harry123180/AUOProject/photo/1651546113493.jpg

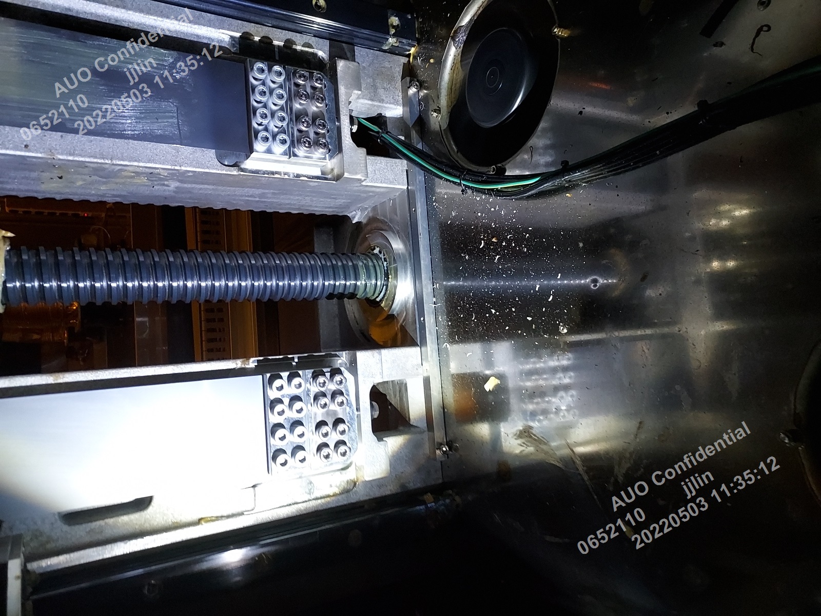
photo/1651546113493.jpg
