harry123180/AUOProject/photo/1651546139501.jpg

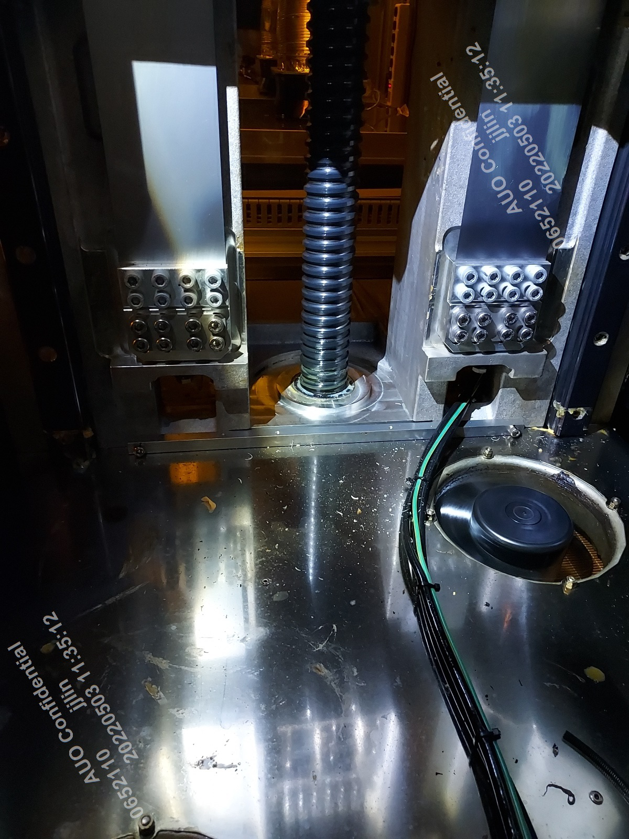
photo/1651546139501.jpg
