harry123180/AUOProject/photo/1651546161636.jpg

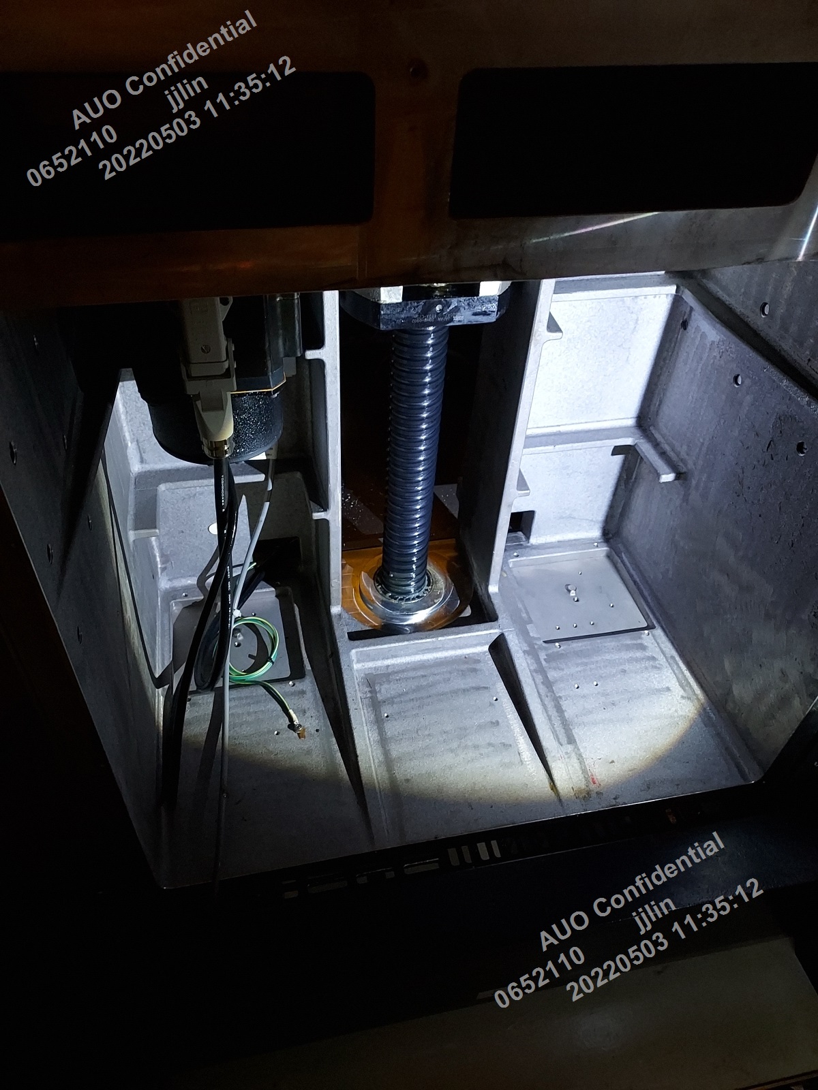
photo/1651546161636.jpg
