harry123180/AUOProject/photo/1651546175267.jpg

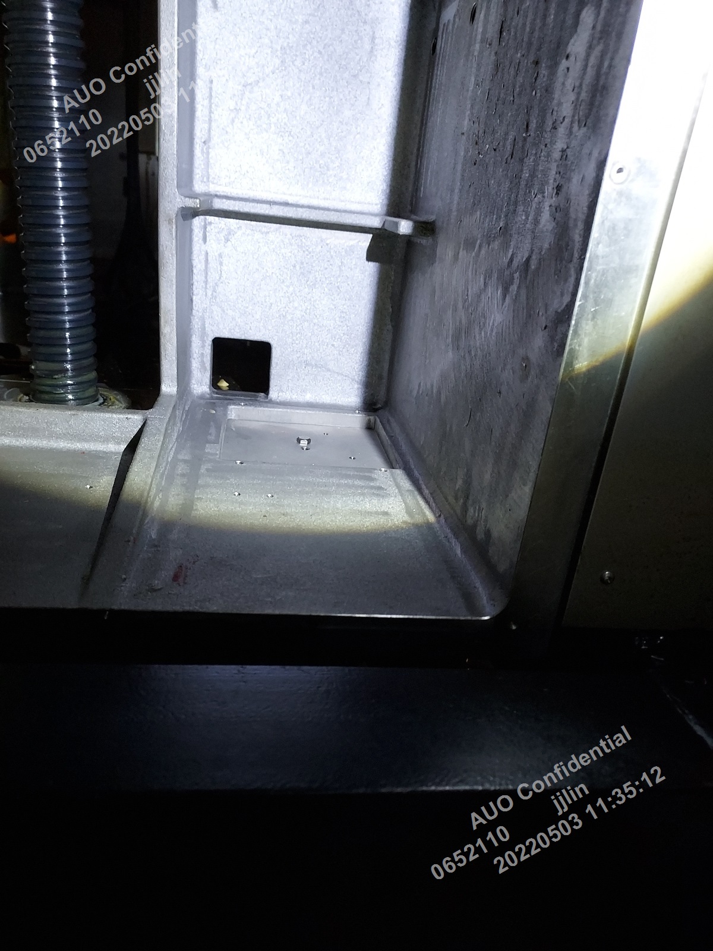
photo/1651546175267.jpg
