harry123180/AUOProject/photo/1651547614620.jpg

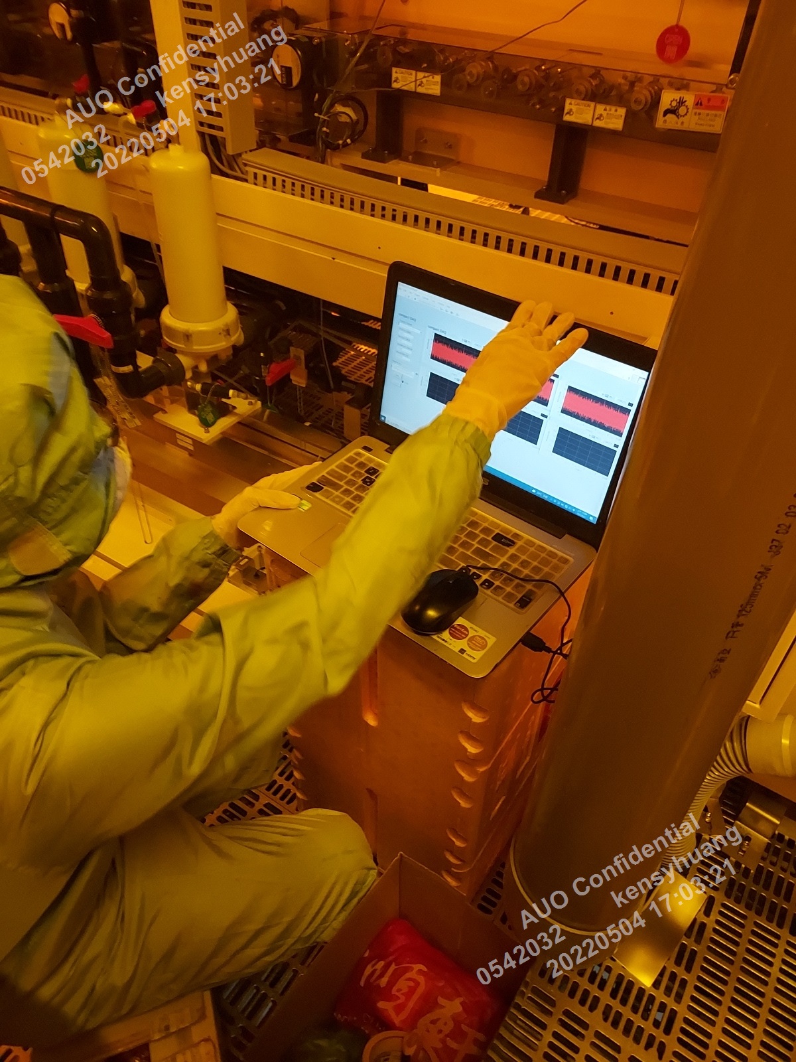
photo/1651547614620.jpg
