harry123180/AUOProject/photo/1651548057626.jpg

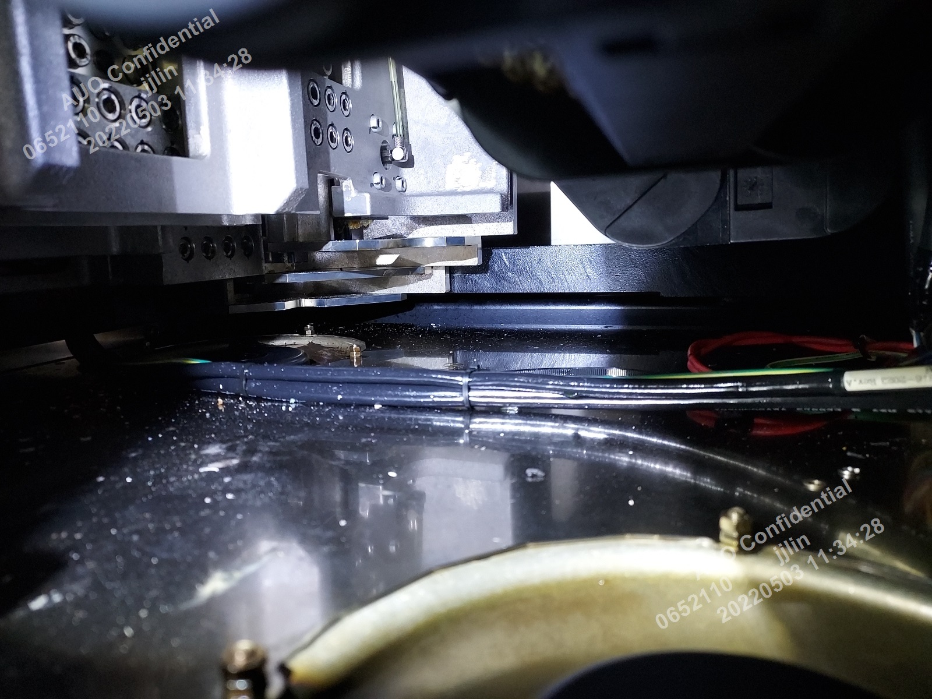
photo/1651548057626.jpg
