harry123180/AUOProject/photo/1651548065328.jpg

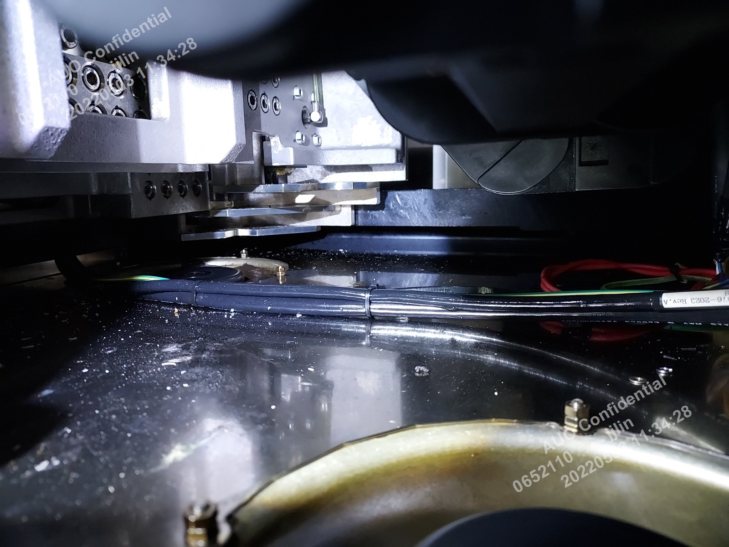
photo/1651548065328.jpg
