harry123180/AUOProject/photo/1651548679285.jpg

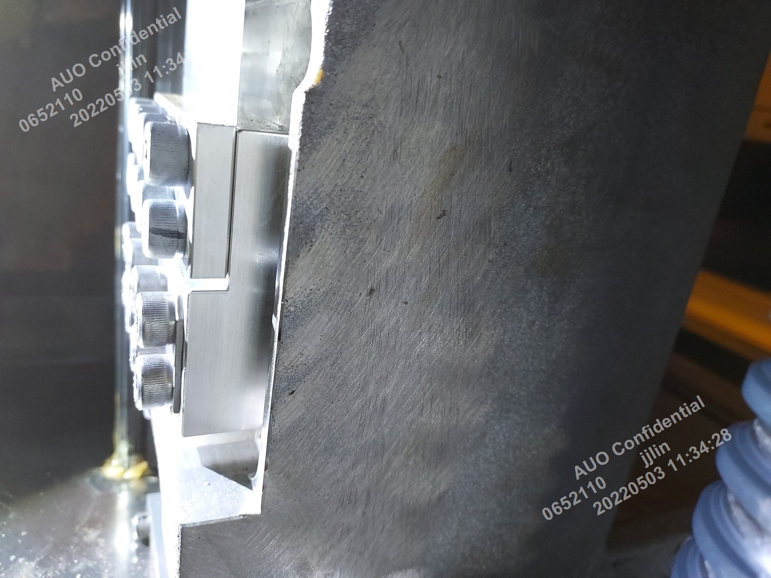
photo/1651548679285.jpg
