harry123180/AUOProject/photo/1651548737667.jpg

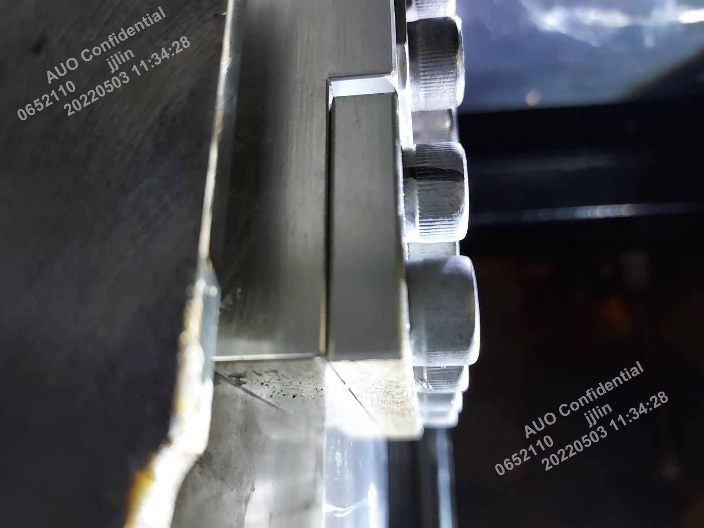
photo/1651548737667.jpg
