harry123180/AUOProject/photo/1651548792946.jpg

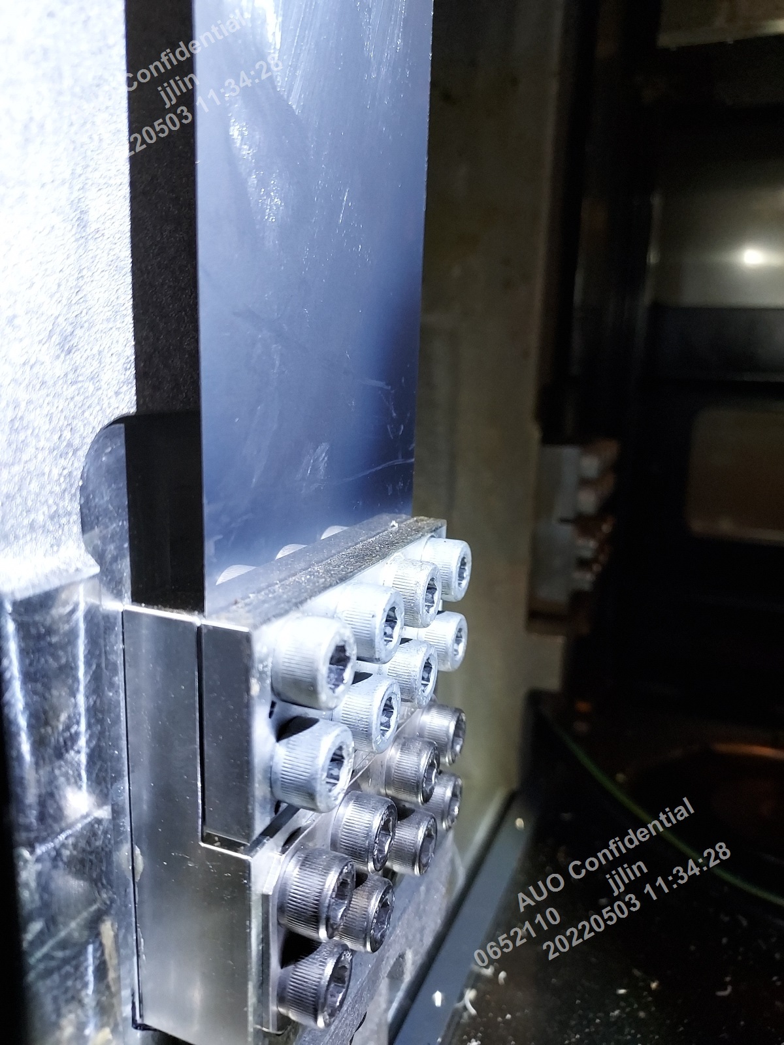
photo/1651548792946.jpg
