harry123180/AUOProject/photo/1651548812156.jpg

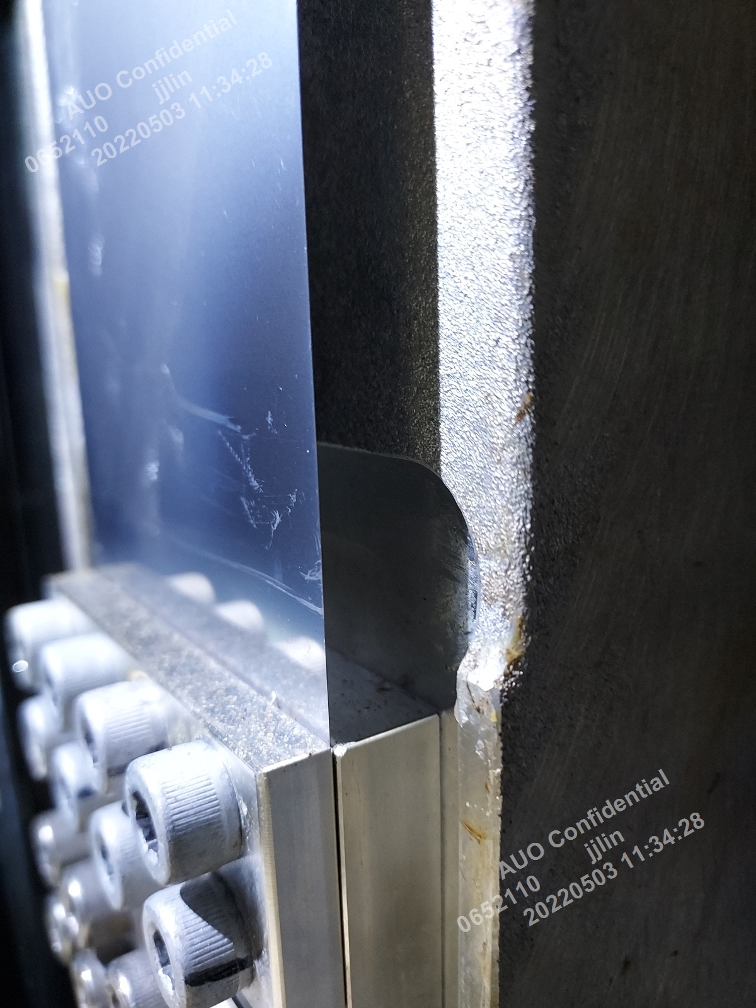
photo/1651548812156.jpg
