harry123180/AUOProject/photo/1651548824308.jpg

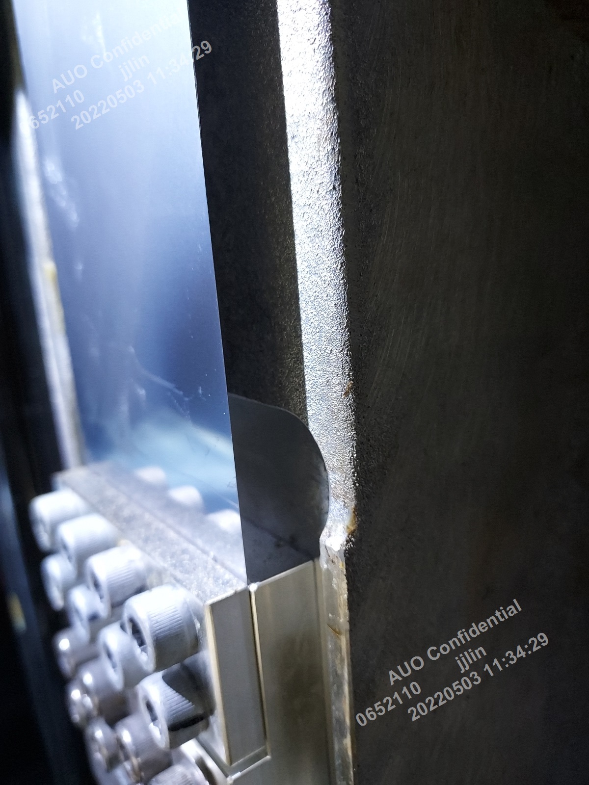
photo/1651548824308.jpg
