harry123180/AUOProject/photo/1651548843207.jpg

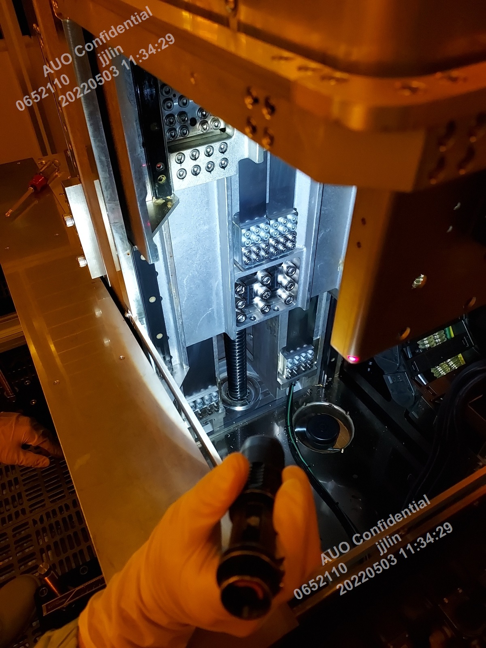
photo/1651548843207.jpg
