harry123180/AUOProject/photo/1651548852555.jpg

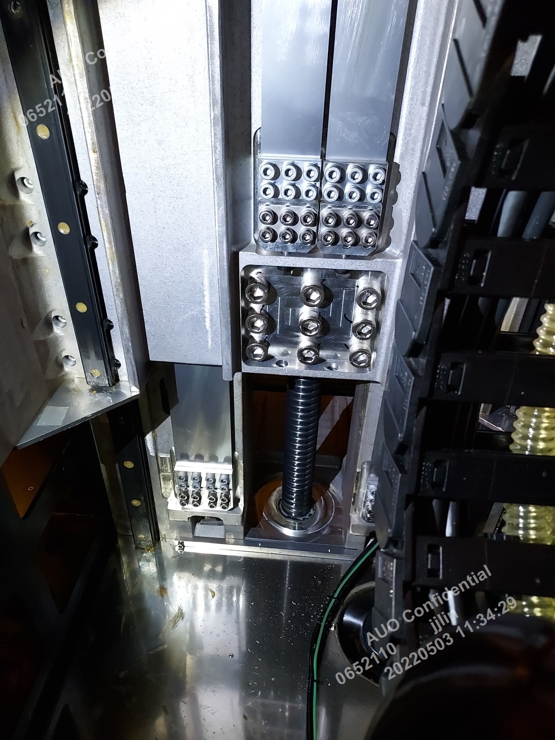
photo/1651548852555.jpg
