harry123180/AUOProject/photo/1651548869333.jpg

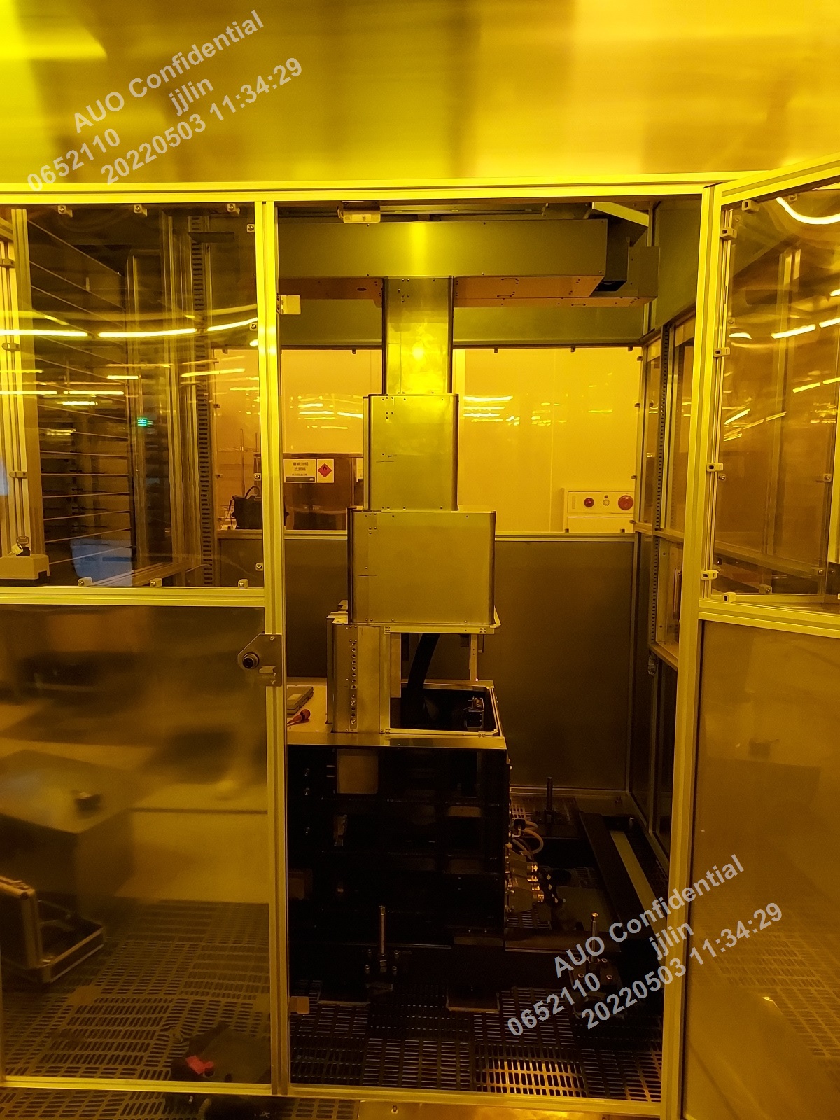
photo/1651548869333.jpg
