harry123180/AUOProject/photo/1651549266964.jpg

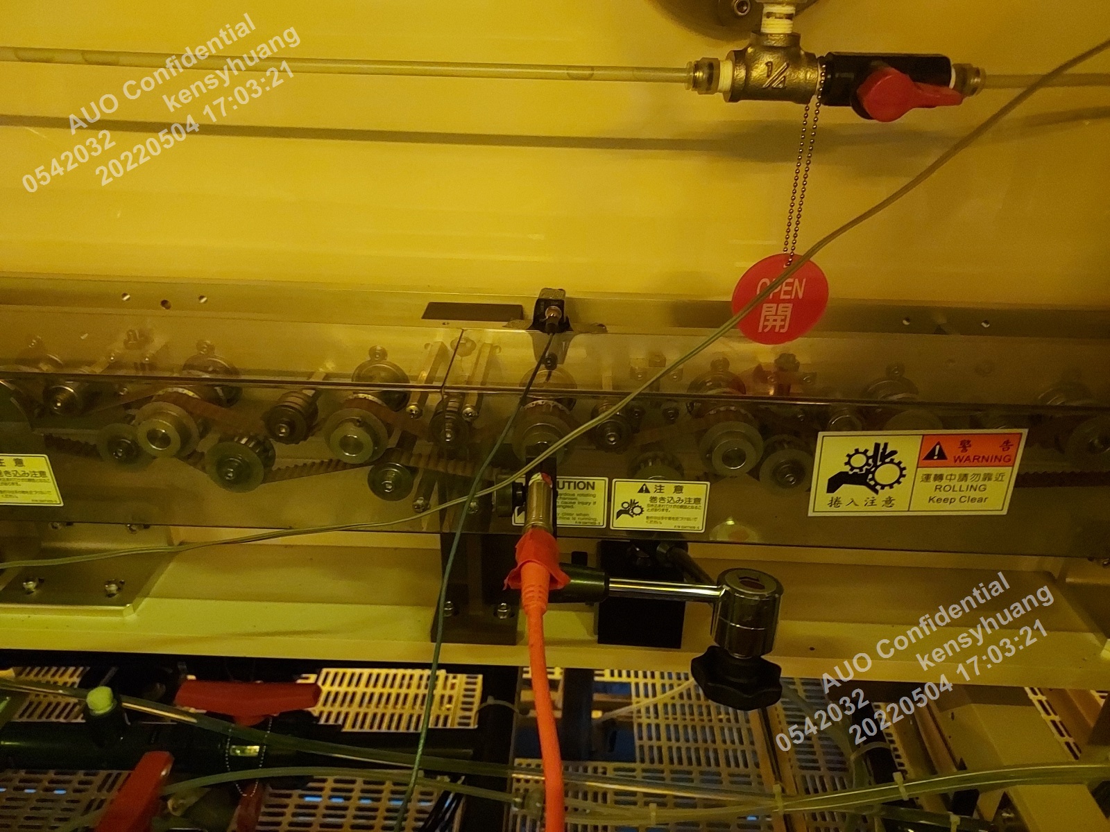
photo/1651549266964.jpg
