harry123180/AUOProject/photo/1651557246759.jpg

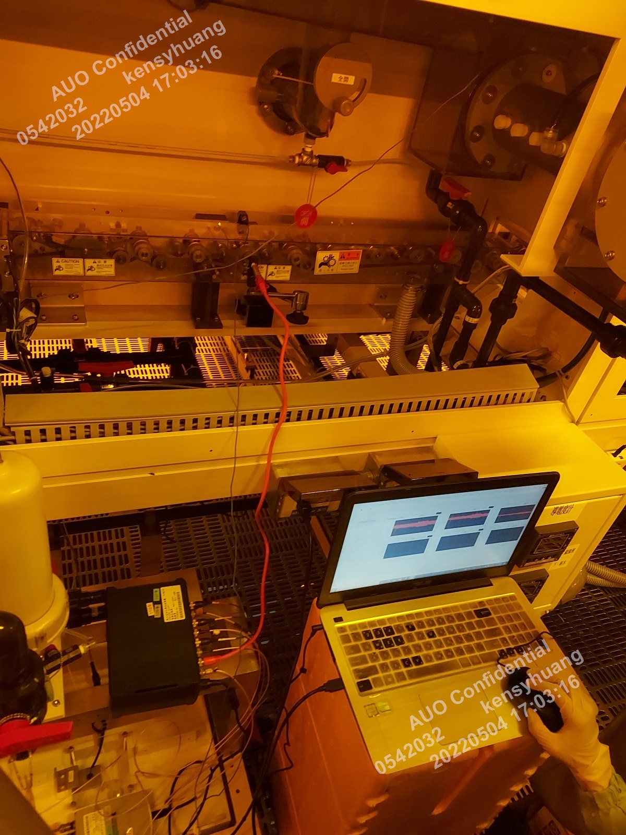
photo/1651557246759.jpg
