harry123180/AUOProject/photo/1651557253789.jpg

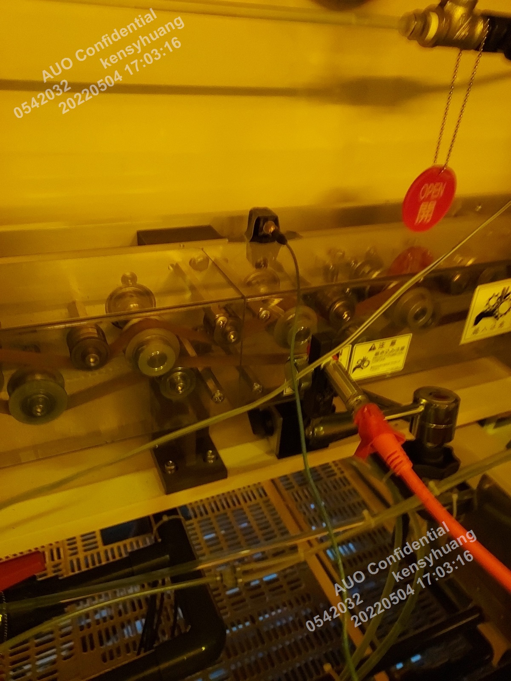
photo/1651557253789.jpg
