harry123180/AUOProject/photo/1651558922676.jpg

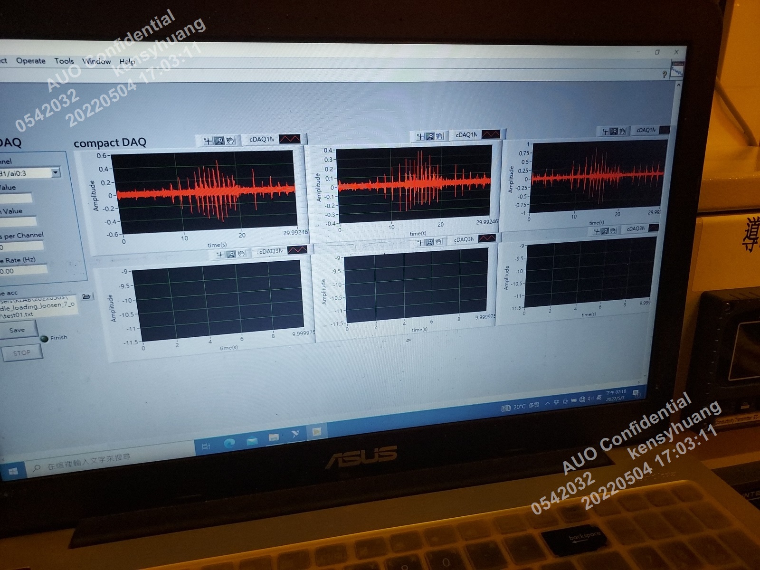
photo/1651558922676.jpg
