harry123180/AUOProject/photo/1651559129728.jpg

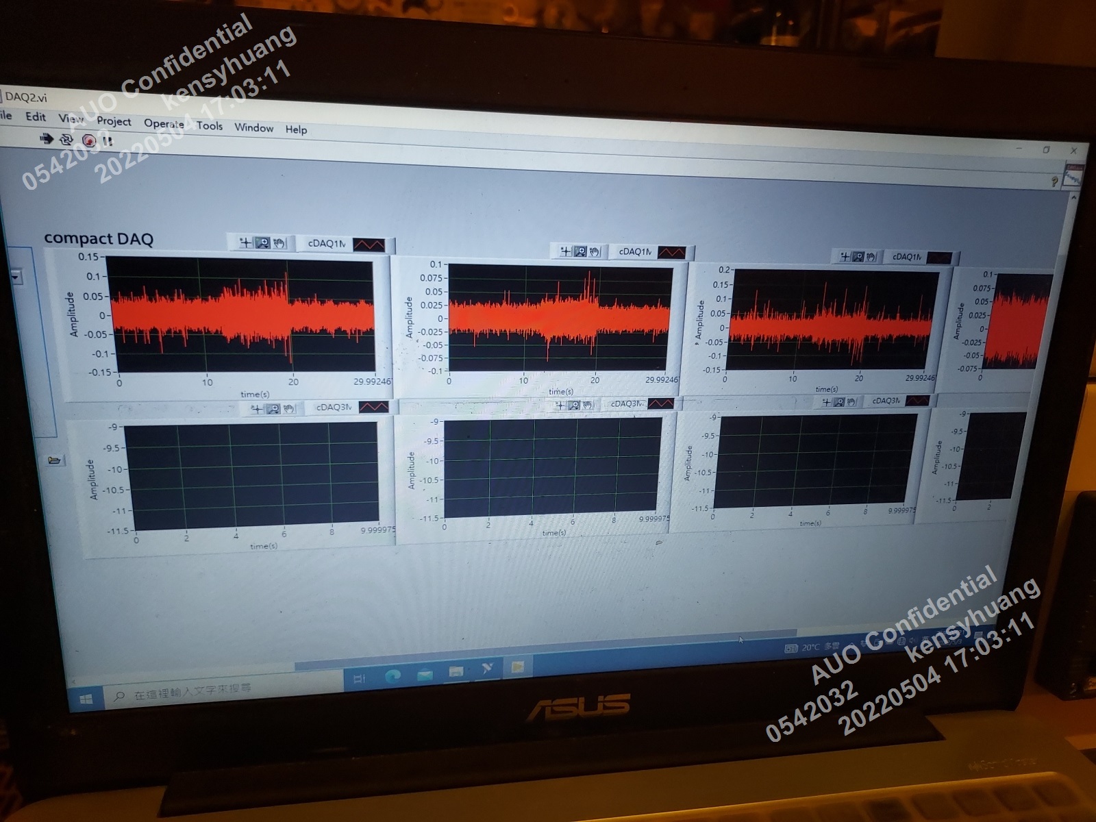
photo/1651559129728.jpg
