harry123180/AUOProject/photo/1651559417045.jpg

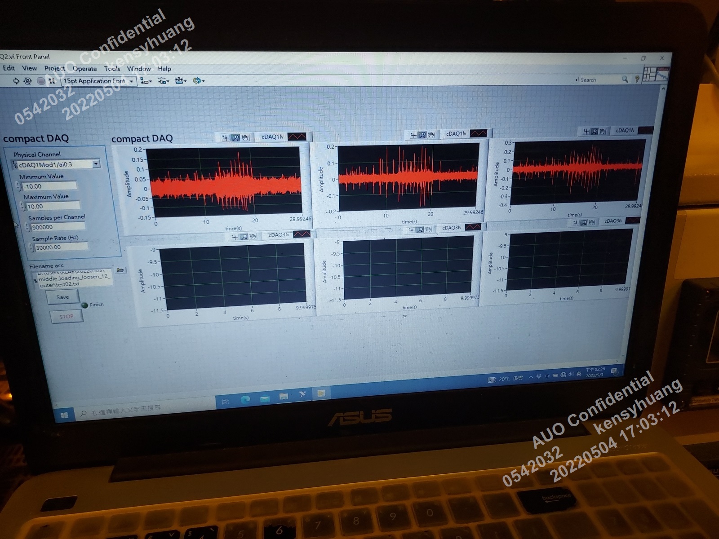
photo/1651559417045.jpg
