harry123180/AUOProject/photo/1651561638030.jpg

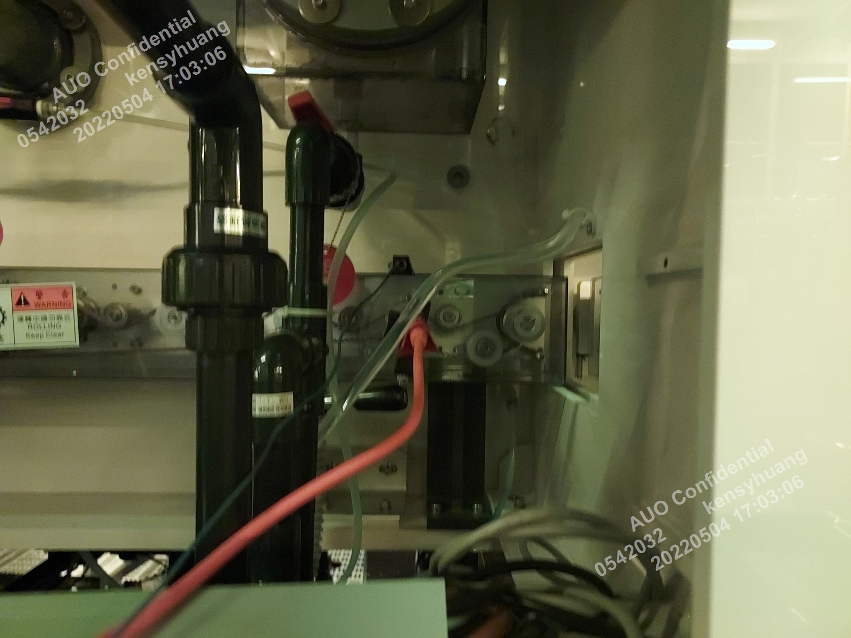
photo/1651561638030.jpg
