harry123180/AUOProject/photo/1651564419721.jpg

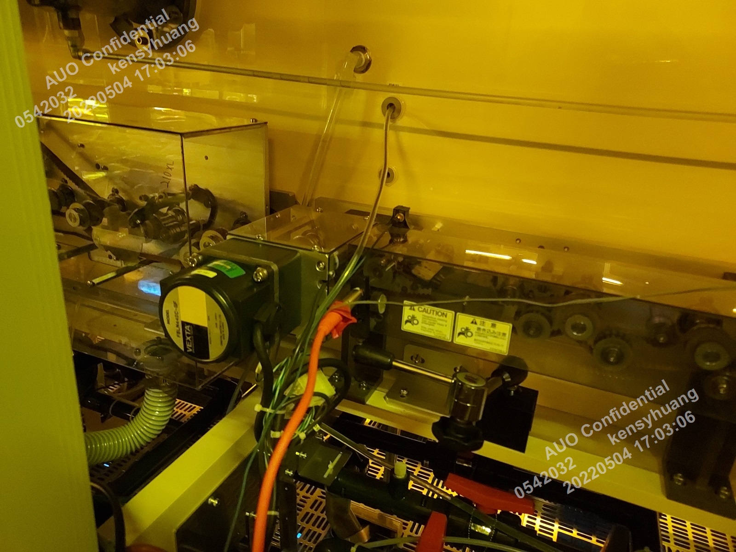
photo/1651564419721.jpg
