harry123180/AUOProject/數據分析圖/C1T.png

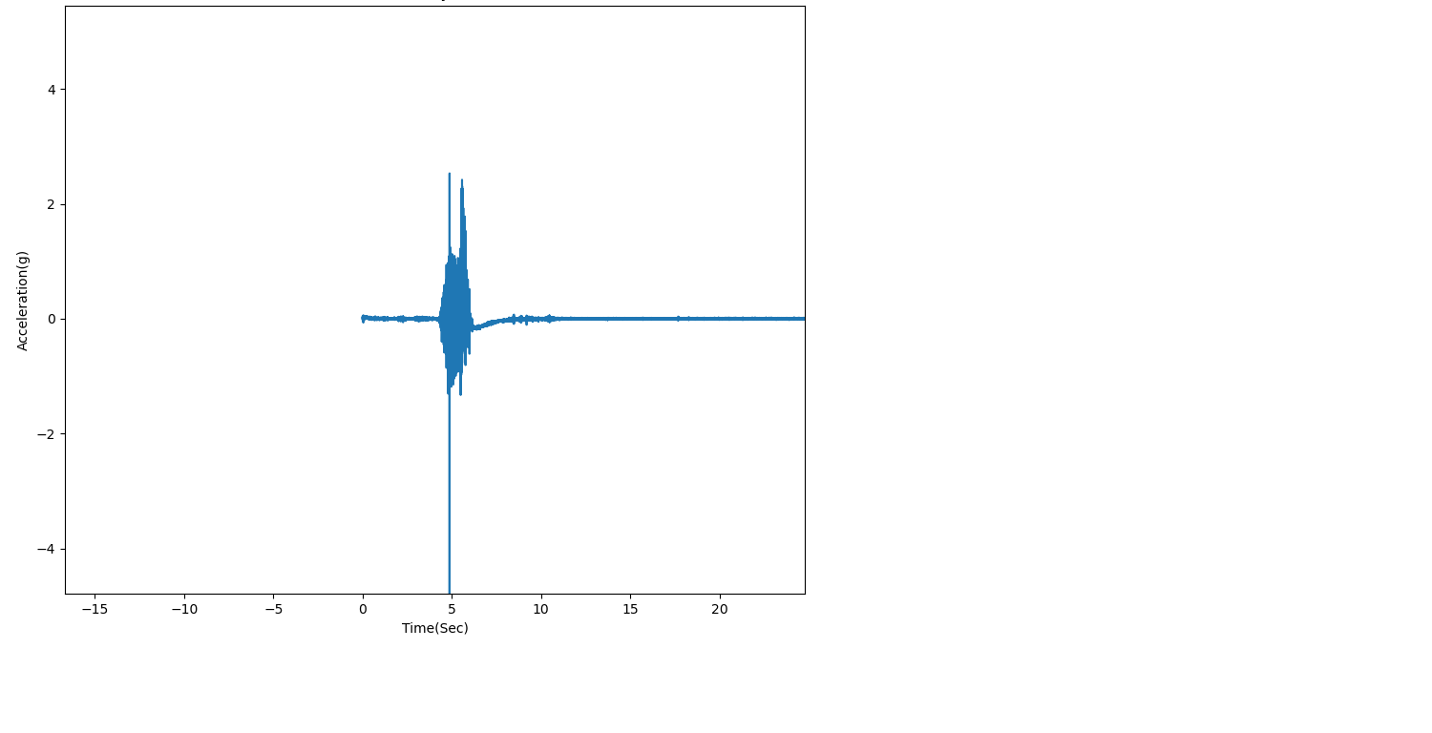
數據分析圖/C1T.png
