harry123180/AUOProject/數據分析圖/C1T_0_30.png

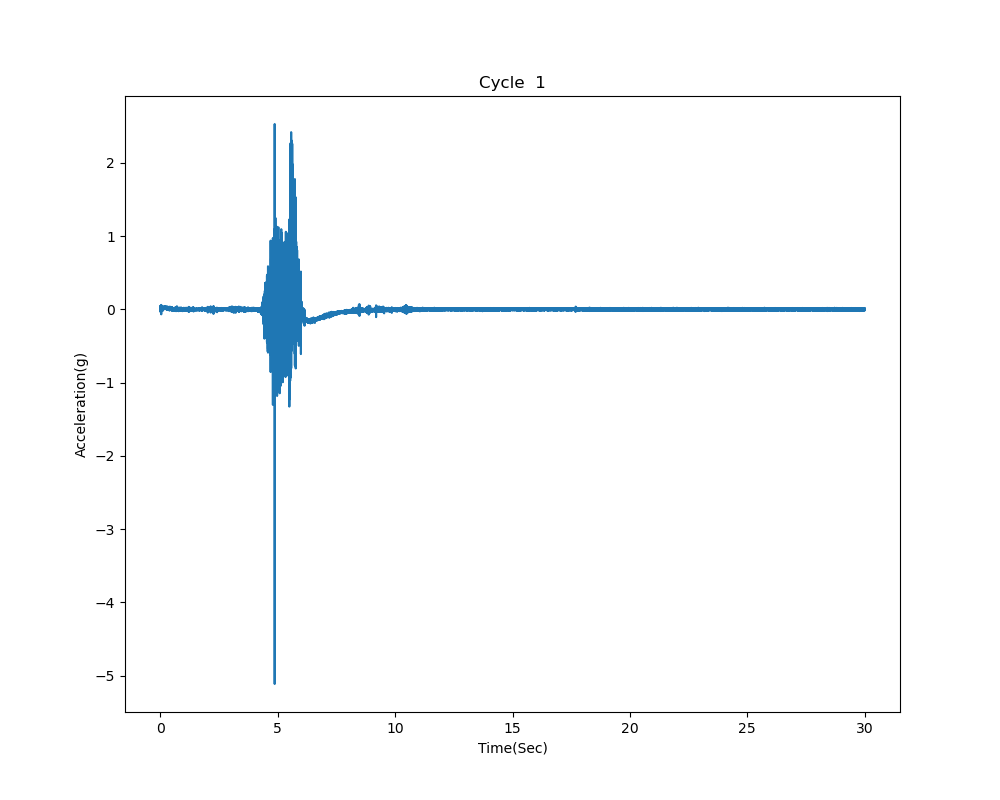
數據分析圖/C1T_0_30.png
