harry123180/AUOProject/數據分析圖/C2_C7_FFT_Mix.png

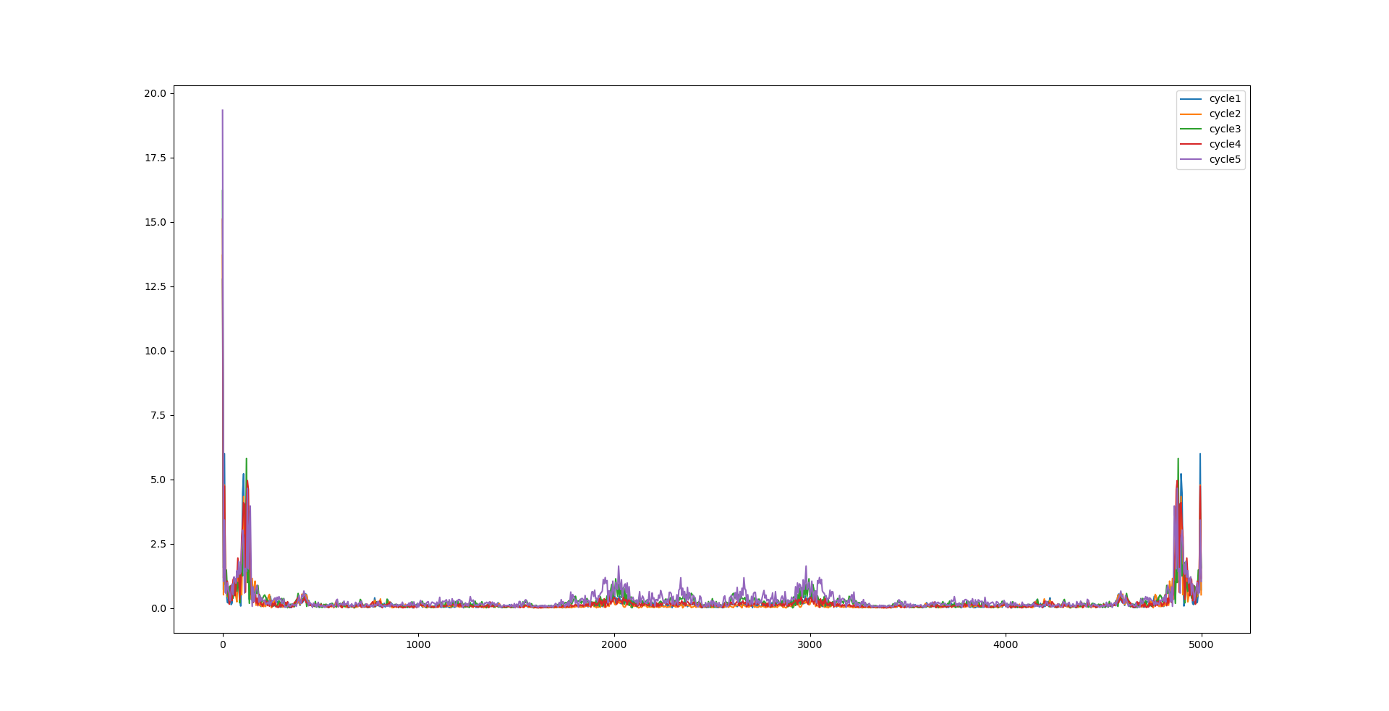
數據分析圖/C2_C7_FFT_Mix.png
