harry123180/AUOProject/數據分析圖/C2T_30_76.png

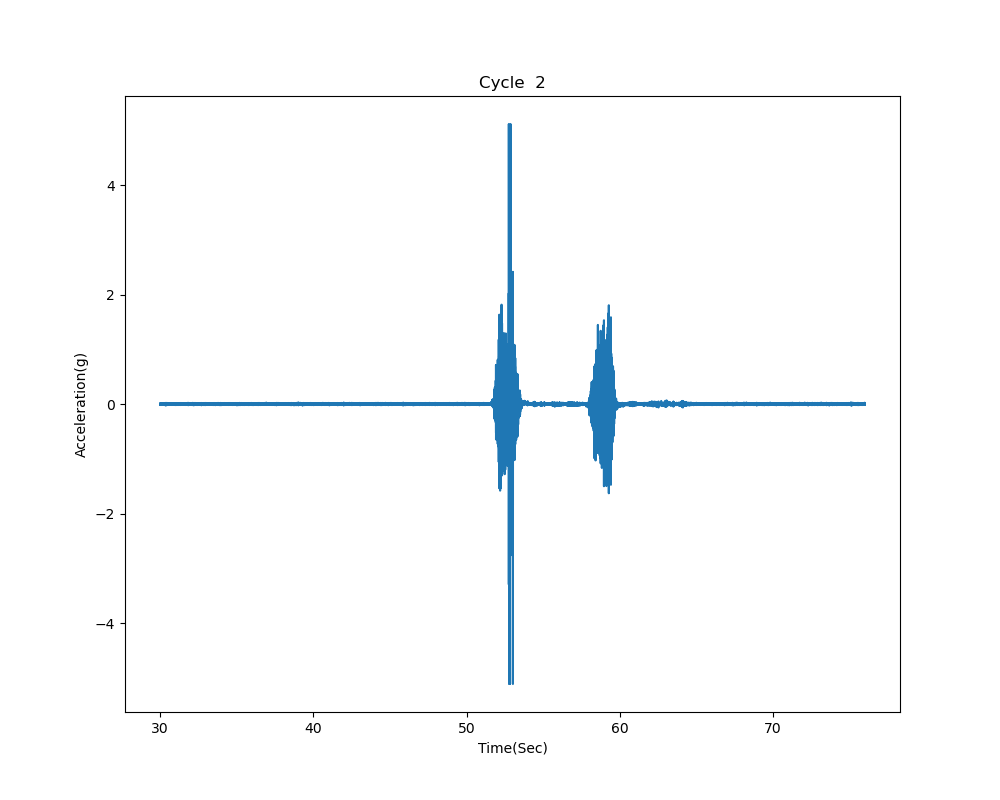
數據分析圖/C2T_30_76.png
