harry123180/AUOProject/數據分析圖/C3T_76_115.png

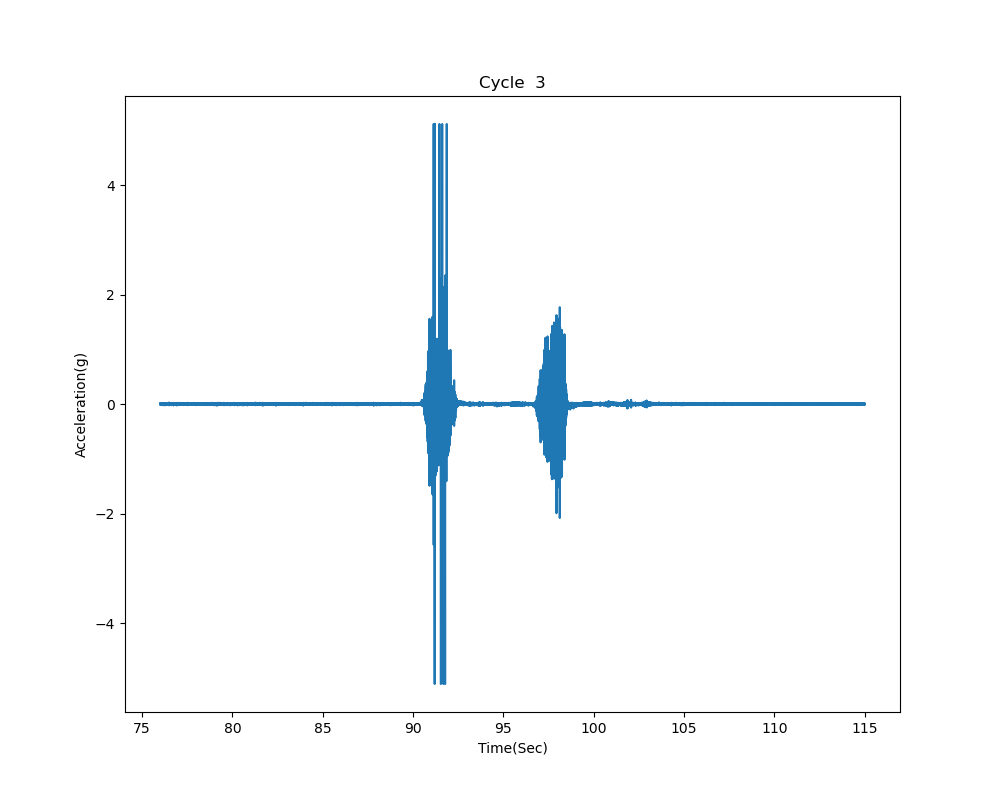
數據分析圖/C3T_76_115.png
