harry123180/AUOProject/數據分析圖/C4T_115_149.png

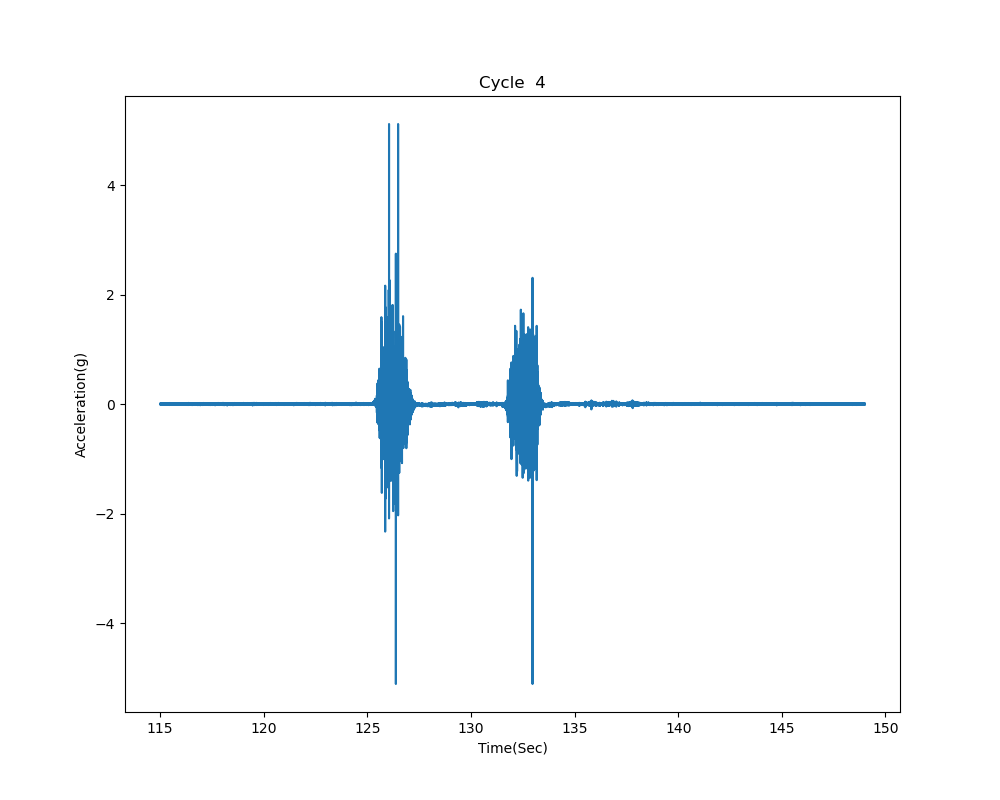
數據分析圖/C4T_115_149.png
