harry123180/AUOProject/數據分析圖/C6_C10_Overlay_Linear.png

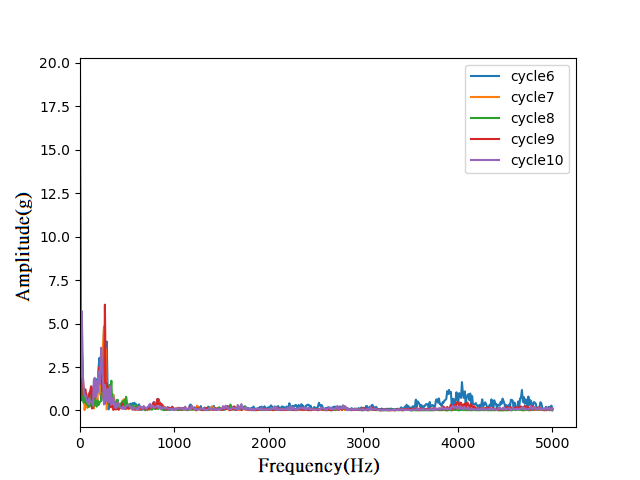
數據分析圖/C6_C10_Overlay_Linear.png
