harry123180/AUOProject/數據分析圖/C6_C10_Overlay_log.png

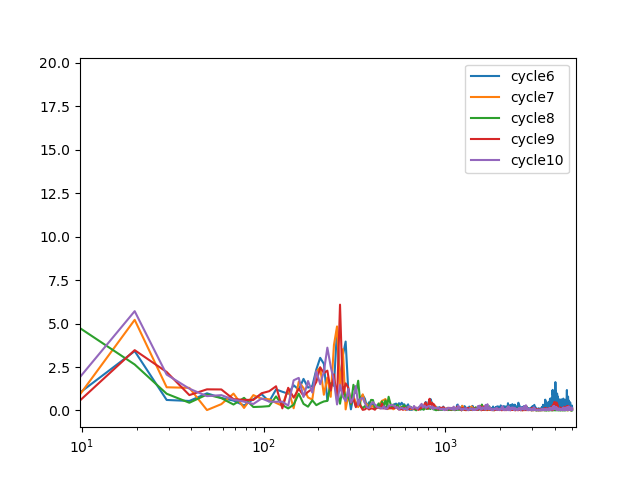
數據分析圖/C6_C10_Overlay_log.png
