harry123180/AUOProject/數據分析圖/C6T_179_217.png

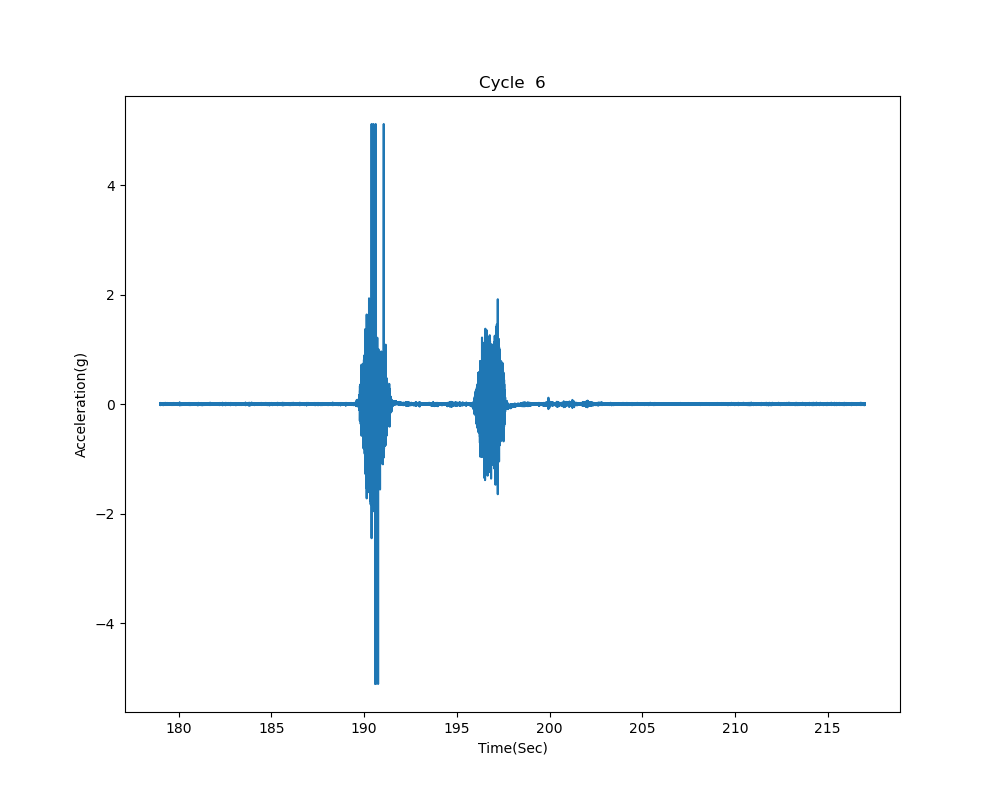
數據分析圖/C6T_179_217.png
