harry123180/AUOProject/數據分析圖/C11_C15_Overlay_log_20k.png

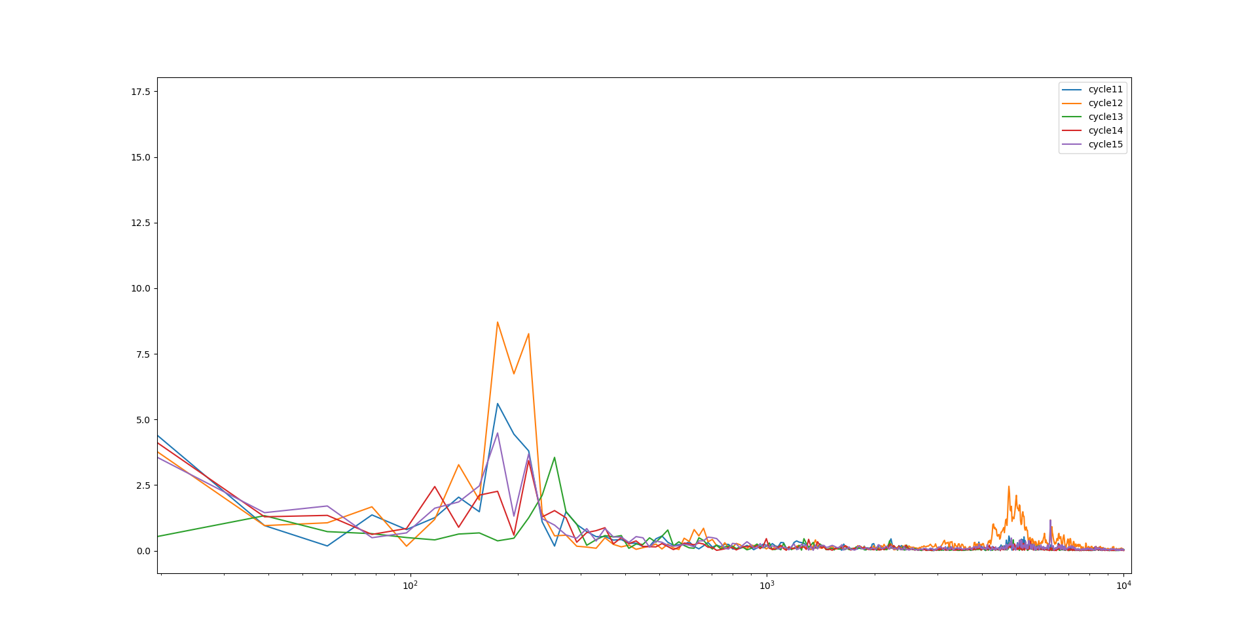
數據分析圖/C11_C15_Overlay_log_20k.png
