harry123180/AUOProject/數據分析圖/C12T_397_435.png

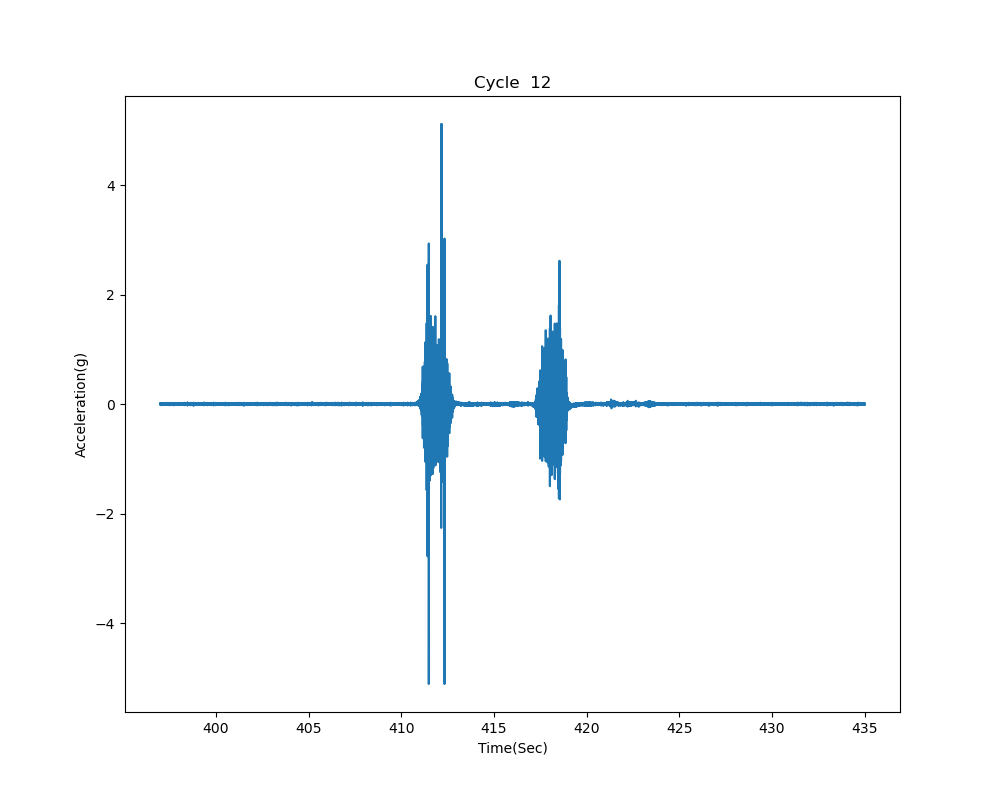
數據分析圖/C12T_397_435.png
