harry123180/AUOProject/數據分析圖/C15T_498_532.png

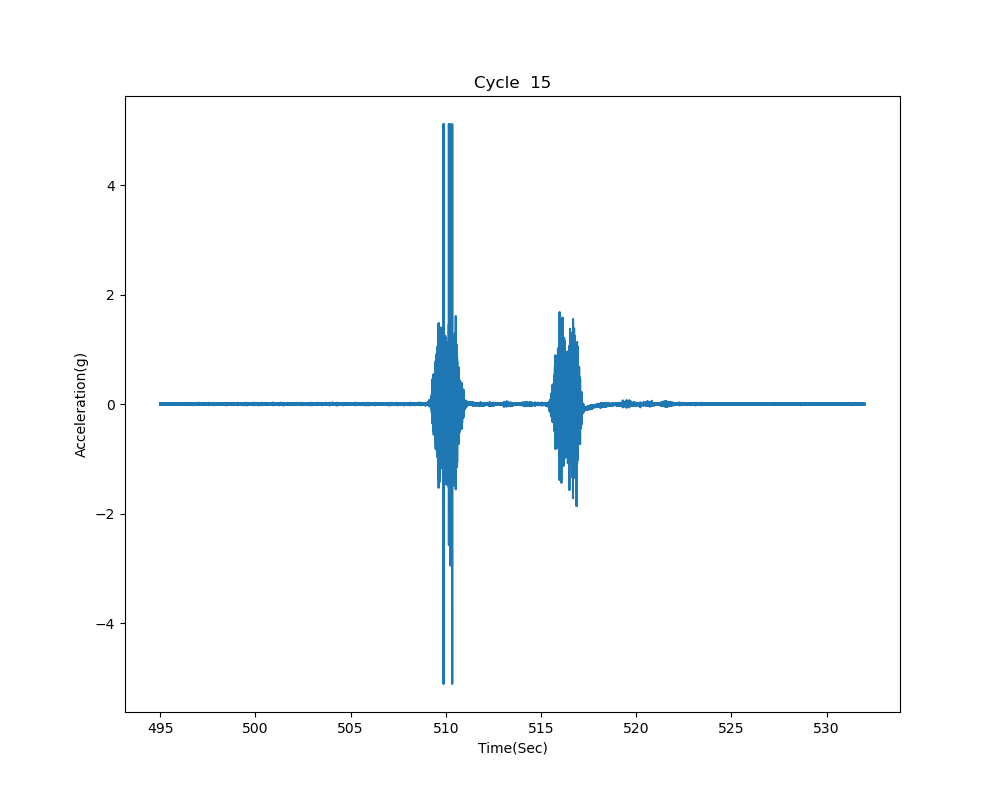
數據分析圖/C15T_498_532.png
