harry123180/AUOProject/數據分析圖/C16T_532_567.png

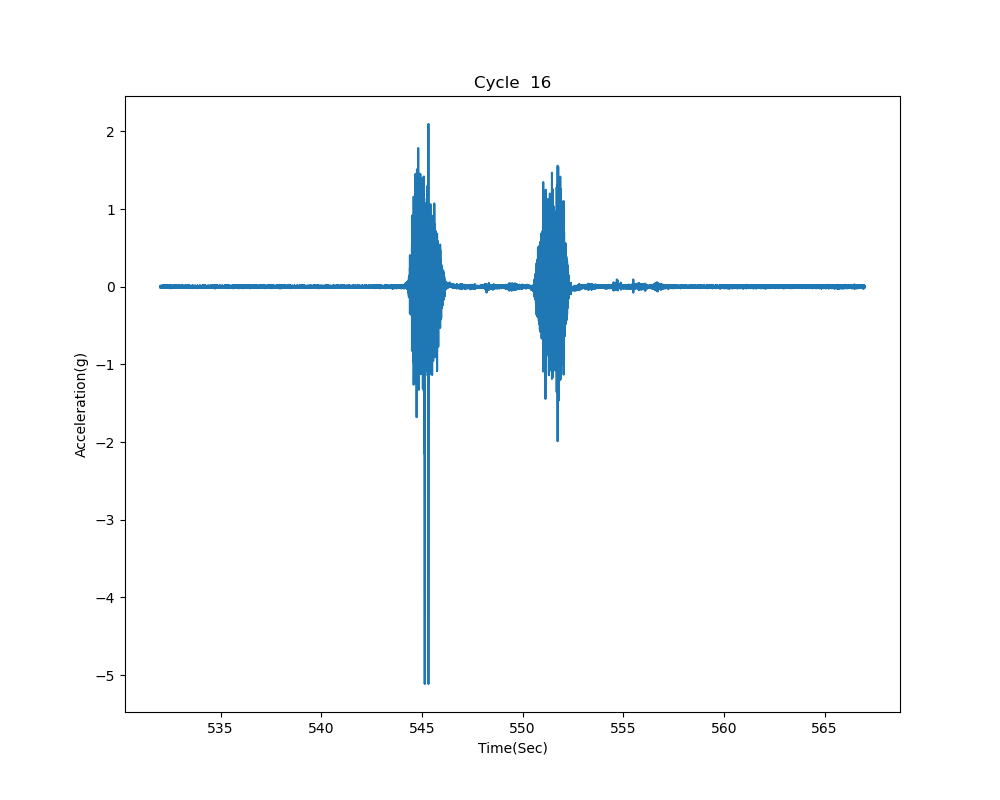
數據分析圖/C16T_532_567.png
