harry123180/AUOProject/數據分析圖/C19T_643_678.png

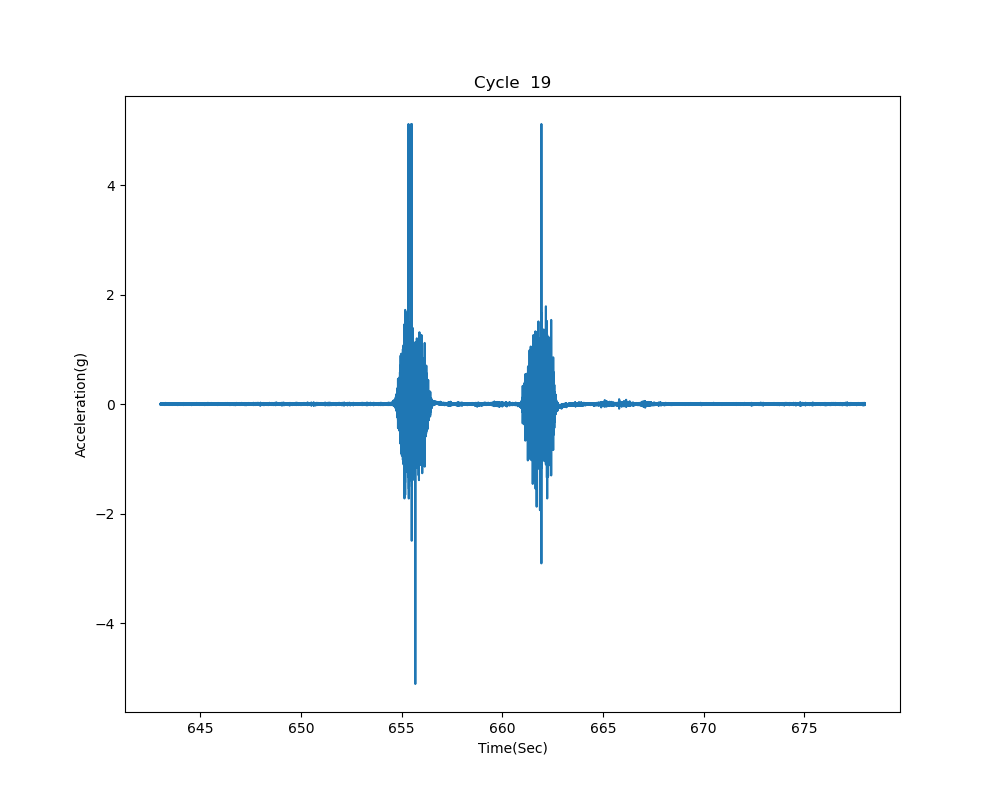
數據分析圖/C19T_643_678.png
