harry123180/AUOProject/數據分析圖/C20T_678_749.png

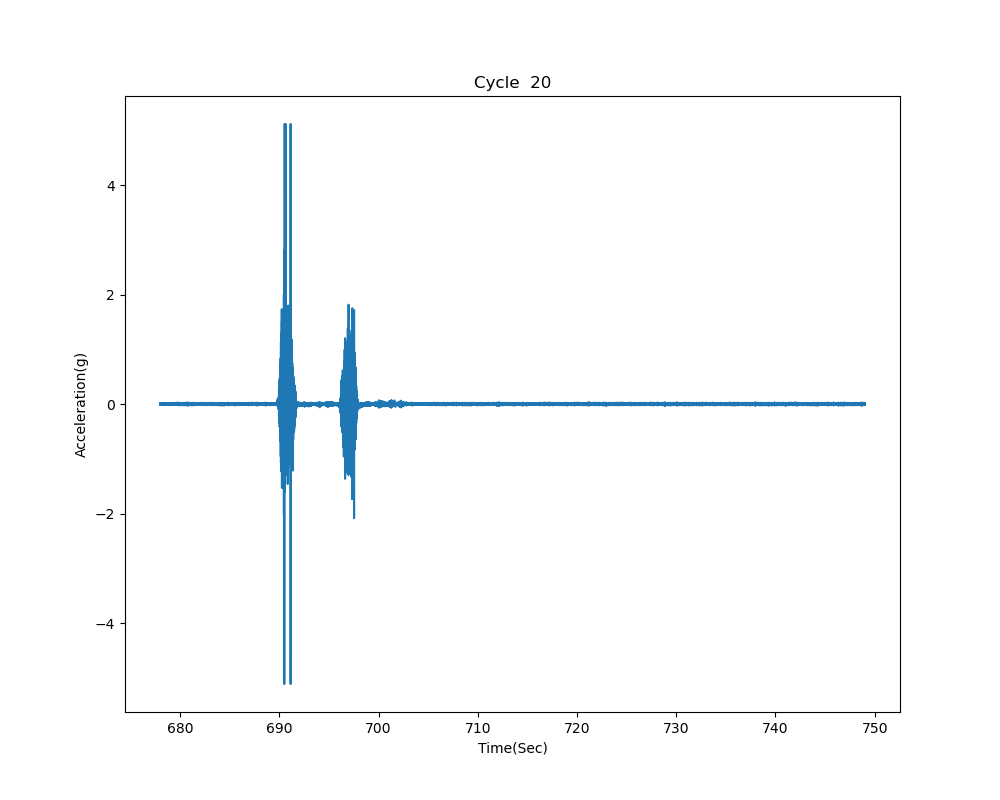
數據分析圖/C20T_678_749.png
