harry123180/AUOProject/數據分析圖/總週期7490000點.png

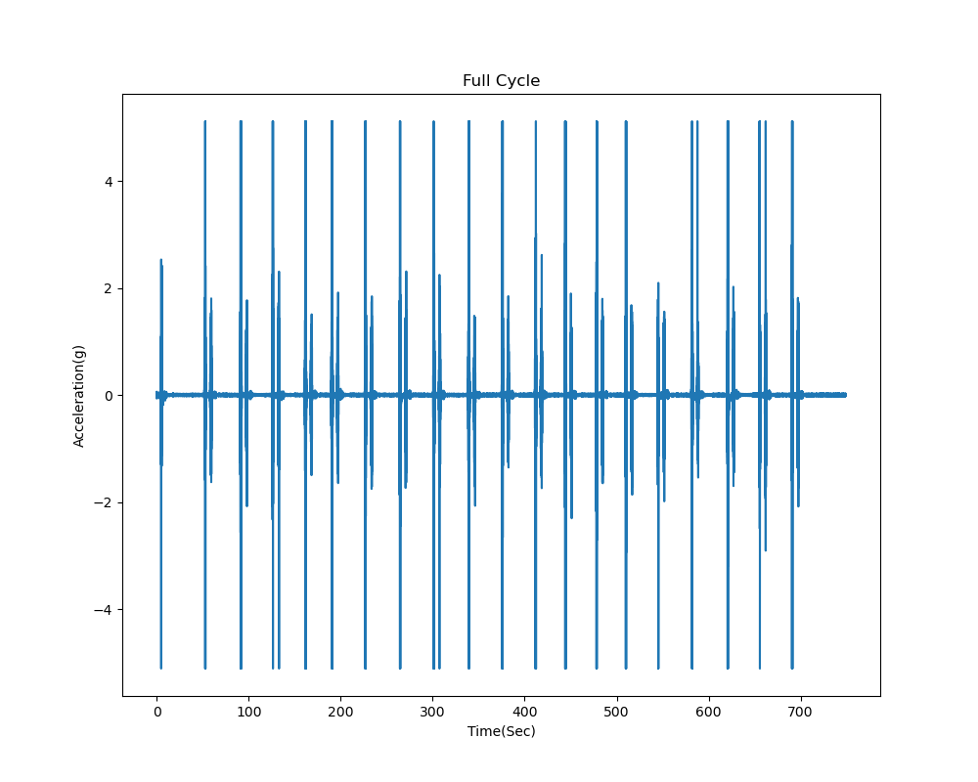
數據分析圖/總週期7490000點.png
