harry123180/AUOProject/upstream/ESP_Program/AUO_Install_Slave/AUO_Install_Slave1/EdgeComputing.h

#ifndef _EDGECOMPUTING_H_
#endif _EDGECOMPUTING_H_
#include <stdlib.h>
#include <stdio.h>
#include <math.h>

class Func{
  public:
  //Func();
  float F1(float v1,float v2);
  float* F2(float* arr1,float* arr2,int Size,float* arr3);
};
class Computer{
  /*初始化Computer物件 在使用前須宣告
  *其內容如下
  *API Document 有詳細說明每個Function的用法及意義
  *[網址]
  */
  private: 
    short int m_FFT_N;
    short int axis_num;
    short int sensitivity;
    short int bias = 1860;
    float K = 3300/sensitivity/4096;
  public:
    Computer(short int FFT_N,short int Quantity_of_Axis,short int value_of_sensitivity );//:m_FFT_N(FFT_N),axis_num(Quantity_of_Axis){}
    void Convert(int* num_data , float* Time_Array);//轉換數值(12bit)到加速度g值換算
    void Convert_2d(int num_data_2d[][1024],float Time_Array[][1024]);//2維轉換式
    //TIme Domain Index 時域指標
    float Mean(float* Time_Array);//平均數
    float Std(float* Time_Array,float avg);//標準差
    float RMS(float* Time_Array);//方均根植
    float Kurtosis(float* Time_Array,float avg,float std);//峰度
    //Frequency Domain Index 頻域指標
    float Total_Power(float* Freq_Array);//總功率
    float ROP(float* Freq_Array,int Freq_min,int Freq_max,float TP);//頻譜強度比例
    /* 二維情況 同時計算多軸數據*/
    //TIme Domain Index 時域指標
    void Mean_2D(float Time_Array[][1024],double* mean_2d);//平均數
    void Std_2D(float Time_Array[][1024],double* avg,double* std_2d);//標準差
    void RMS_2D(float Time_Array[][1024],double* rms_2d);//方均根植
    void Kurtosis_2D(float Time_Array[][1024],double* avg,double* std,double* kurtosis_2d);//峰度
    //Frequency Domain Index 頻域指標
    void Total_Power_2D(float Freq_Array[][512],double* total_power_2d);//總功率
    void ROP_2D(float Freq_Array[][512],int* Freq_min,int* Freq_max,double* TP,double* rop_2d);//頻譜強度比例
};
